PMheiilsDev/midi_test/midi_test.c

#pragma region includes

#include <stdlib.h>
#include <stdio.h>
#include <string.h>

#include "pico/stdio.h"
#include "pico/stdlib.h"
#include "pico/time.h"

#include "hardware/gpio.h"
#include "hardware/adc.h"
#include "hardware/pwm.h"

#include "bsp/board_api.h"
#include "tusb.h"

#include "rotarty_switch.h"
#include "midi_handler.h"
#include "adc_handler.h"
#include "led_handler.h"
#include "ws2812.h"
#include "ws2812_handler.h"
#include "IOexpander.h"
#include "IOexpander_handler.h"

#include "pico/time.h"



#pragma endregion

//#include "pico/gpio.h"

#pragma region defines



#pragma endregion

//void rot_sw_setup(void);

void button_task(void);

uint ctr = 0; 

uint64_t loop_time = 0;
uint64_t loop_time_pref = 0;

uint64_t loop_time_res = 0;

/*------------- MAIN -------------*/
int main(void)
{
    ws2812_setup();

    IO_expander_handler_init();

    led_setup();
    adc_setup();
    rot_sw_setup();
    // init device stack on configured roothub port
    tud_init(BOARD_TUD_RHPORT);

    char data [640*4];
    char temp[12];
    sprintf(temp,"%x",data);
    for( int i = 0; i < 640*4; i++ )
    {
        data[i] = 0; 
    }

    buffer = malloc( 0x100 * 128 * sizeof(char) );

    
    while (1)
    {
        loop_time_pref = loop_time;
        loop_time = time_us_64();
        loop_time_res = loop_time-loop_time_pref;
        
        process_midi_message(); 

        tud_task(); // tinyusb device task
        button_task();
        adc_task();
        rot_sw_task();
        ws2812_task();

        IOexpander_task();
        IO_expander_handler_handler();
    }
}
